bitmerse/WiSer/docs/wiser-product-manual/further-support/README.md

# Further Support

### Customer Support Contact 

If you require assistance or have questions not covered in this manual, please contact our customer support team:

* Email: [support@bitmerse.com](mailto:support@bitmerse.com)
